Ramana-bharathi/satellite-housing-design-manufacturing/Drawings/DWG pics/Housing_bottom.jpg

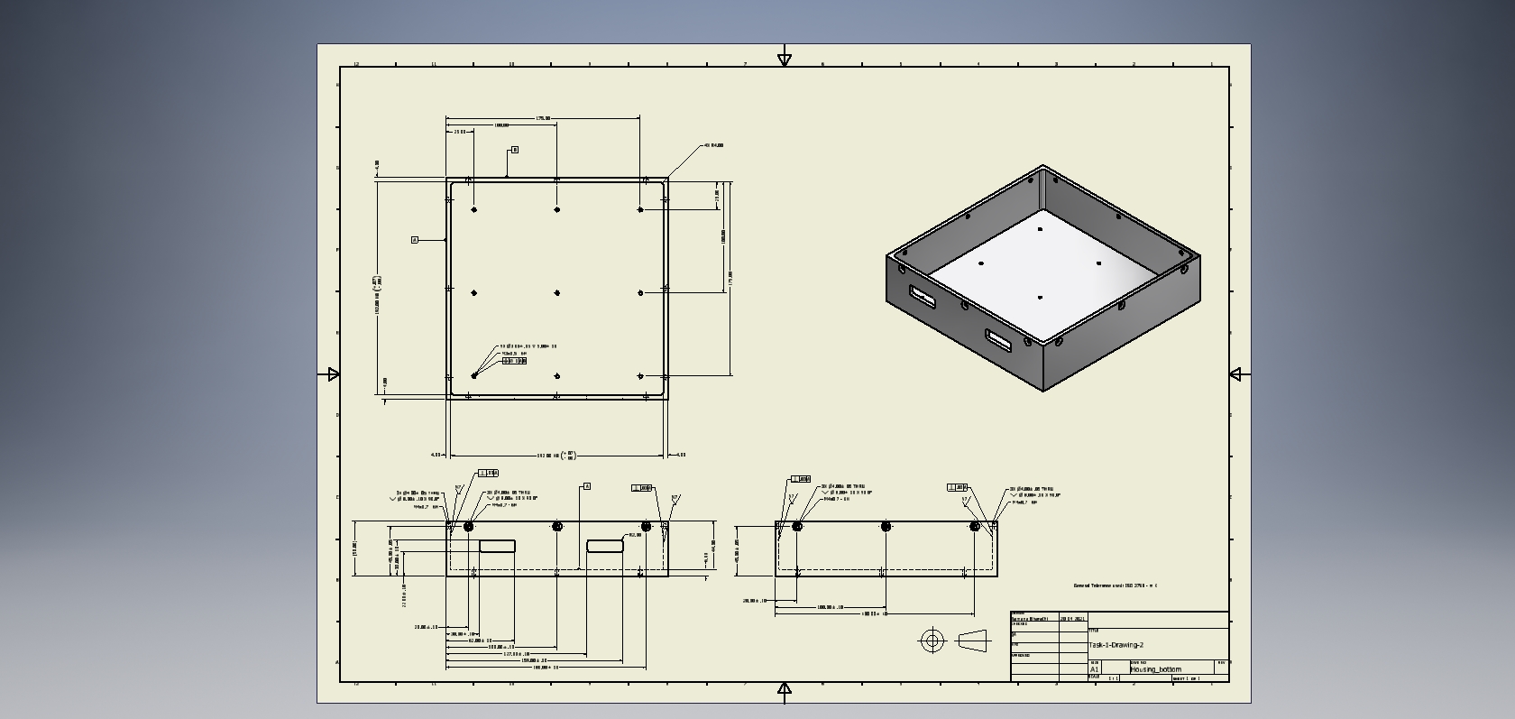
Drawings/DWG pics/Housing_bottom.jpg
