Ramana-bharathi/satellite-housing-design-manufacturing/Drawings/DWG pics/Housing_lid.jpg

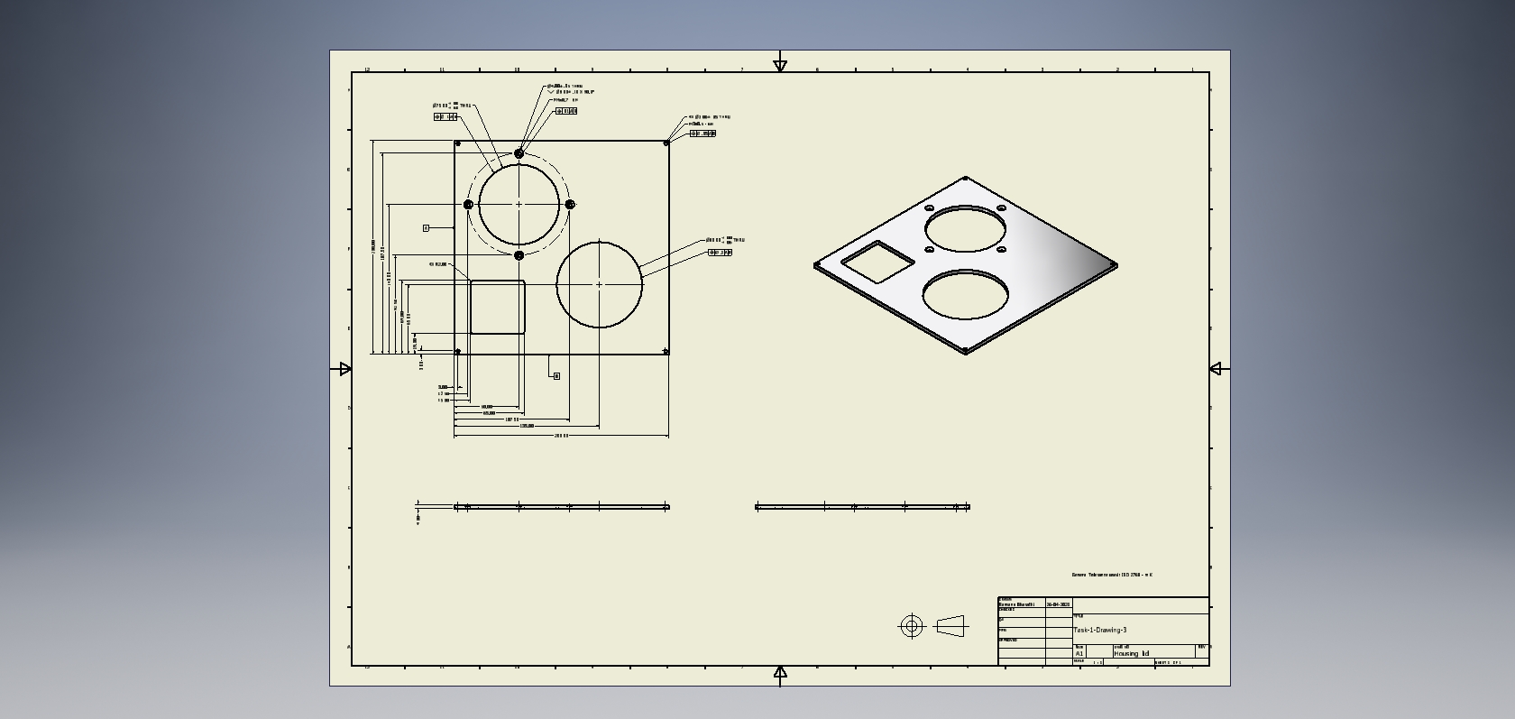
Drawings/DWG pics/Housing_lid.jpg
