Ramana-bharathi/satellite-housing-design-manufacturing/Drawings/DWG pics/Housing_top.jpg

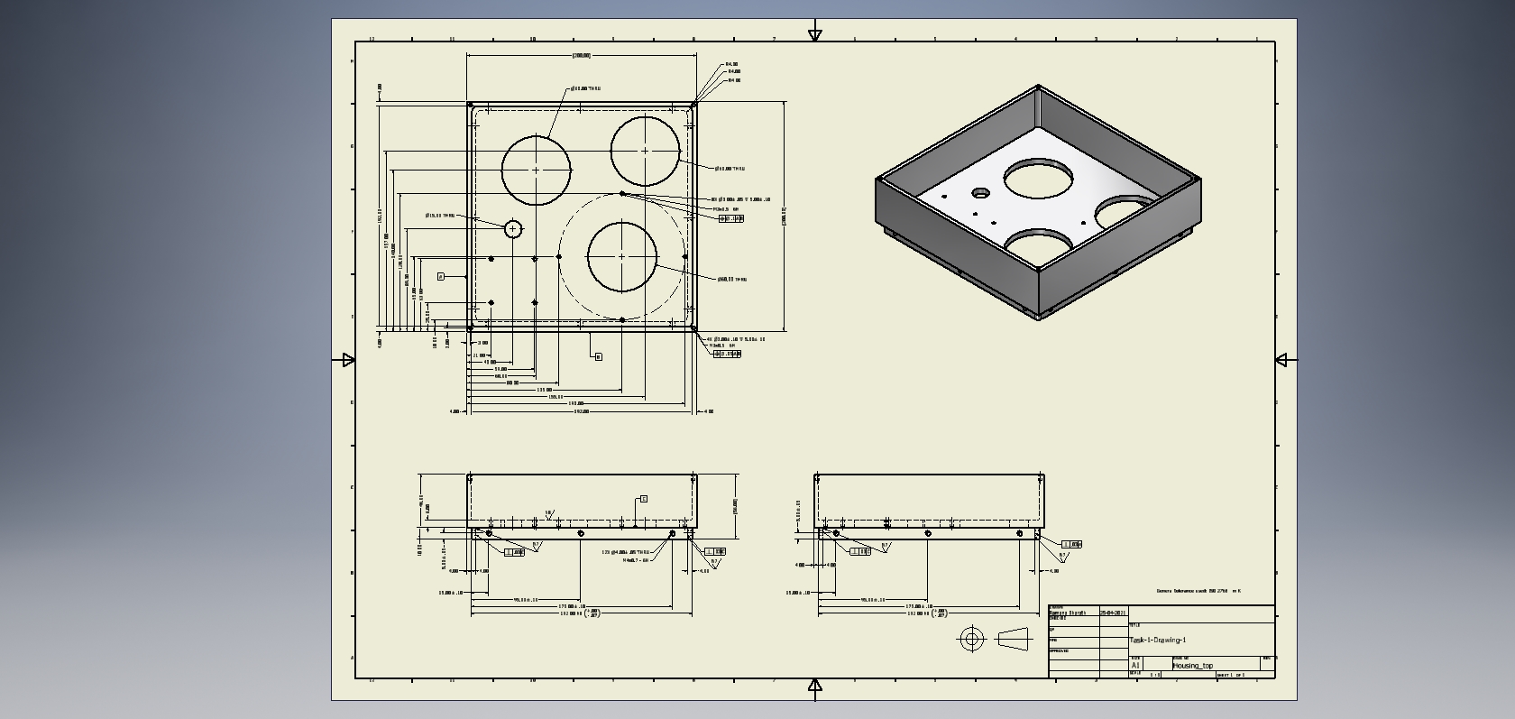
Drawings/DWG pics/Housing_top.jpg
