Ramana-bharathi/satellite-housing-design-manufacturing/Drawings/DWG pics/sensor1_lock.jpg

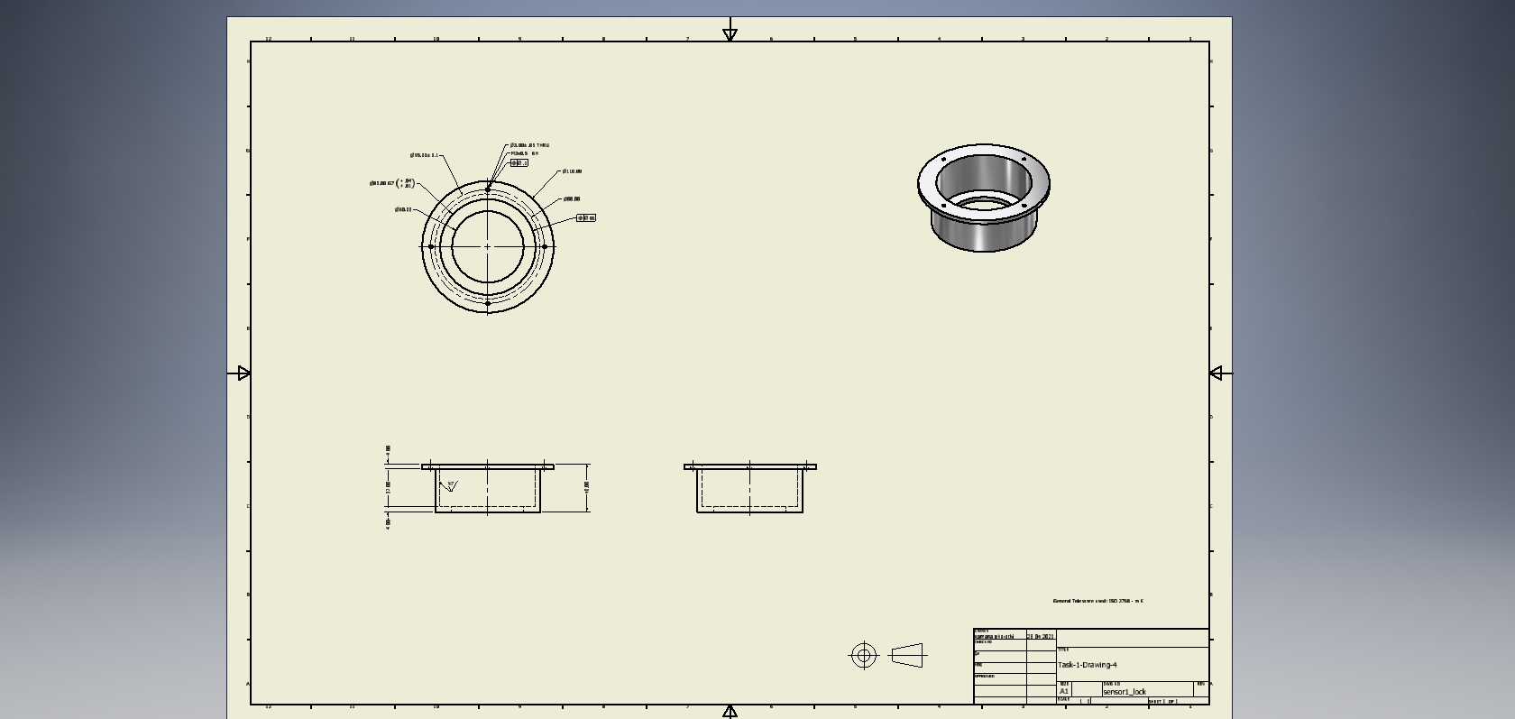
Drawings/DWG pics/sensor1_lock.jpg
