Ramana-bharathi/satellite-housing-design-manufacturing/Drawings/DWG pics/sensor2_lock.jpg

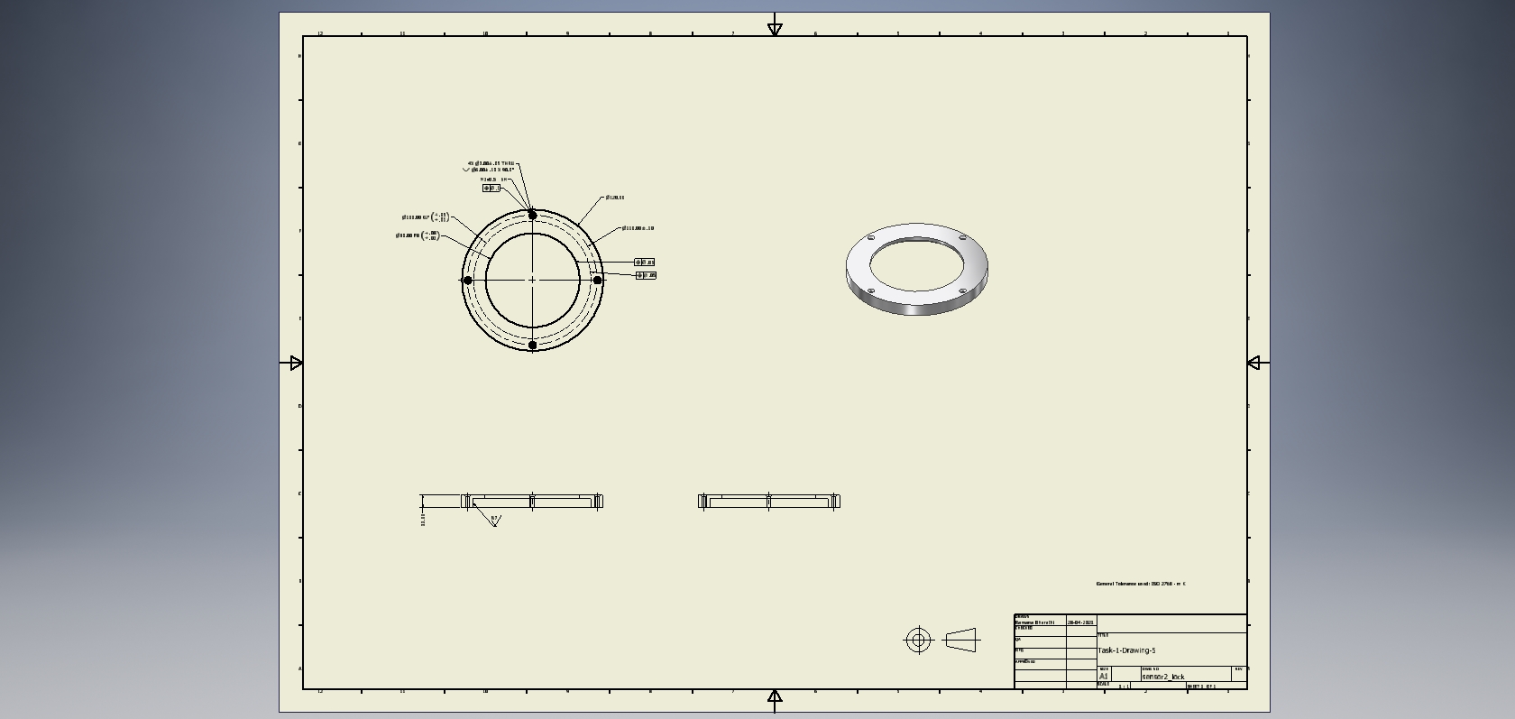
Drawings/DWG pics/sensor2_lock.jpg
