Ramana-bharathi/satellite-housing-design-manufacturing/Drawings/DWG pics/sensor3_lock.jpg

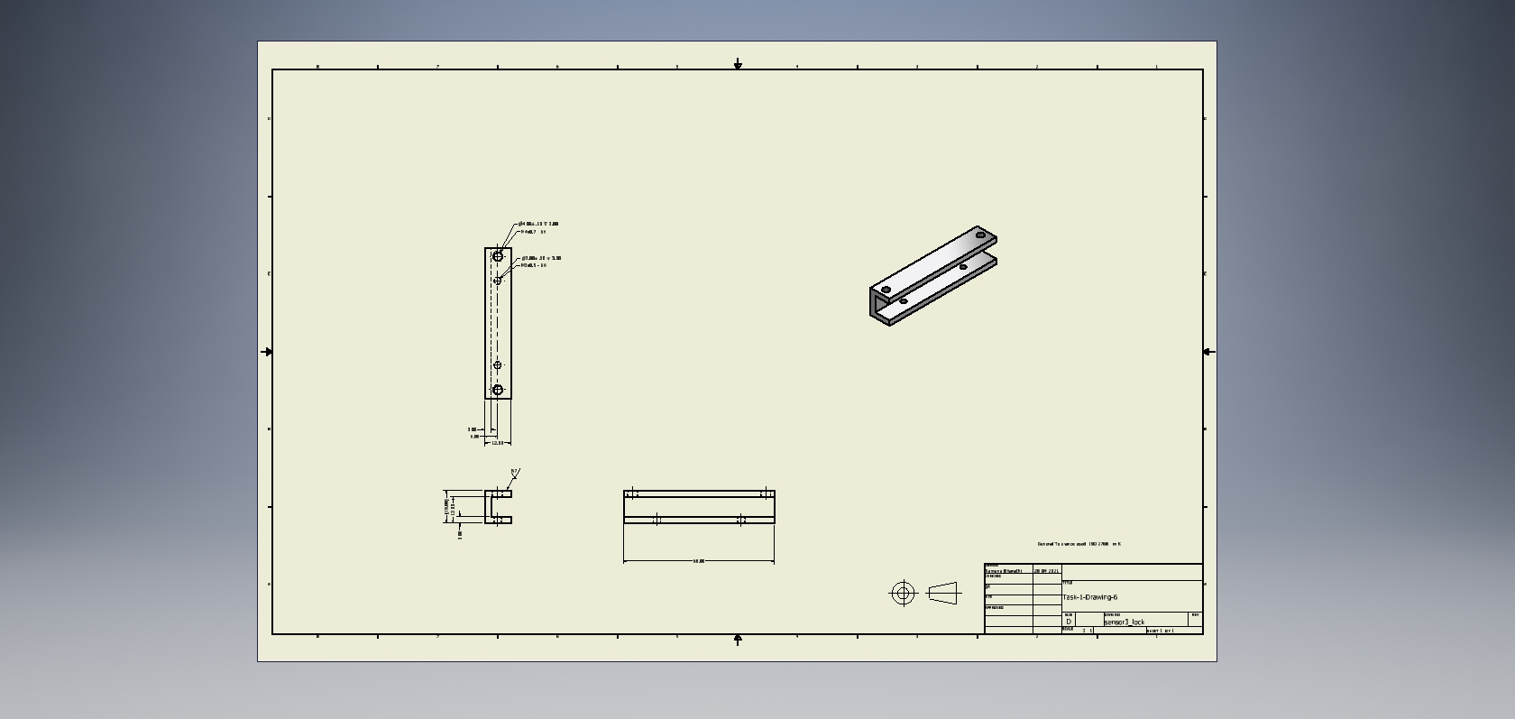
Drawings/DWG pics/sensor3_lock.jpg
