Ramana-bharathi/satellite-housing-design-manufacturing/Machining sequences/pics/housing_bottom-3.jpg

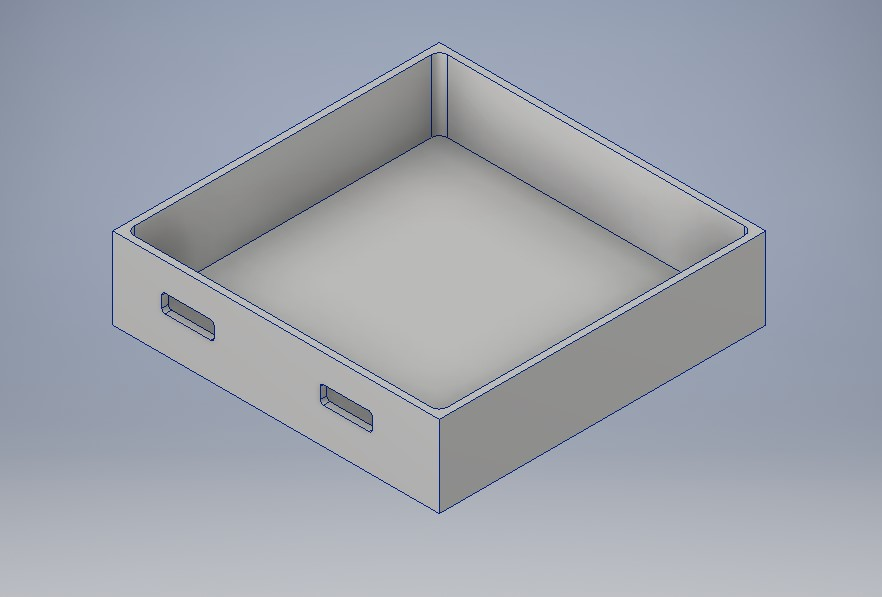
Machining sequences/pics/housing_bottom-3.jpg
