Ramana-bharathi/satellite-housing-design-manufacturing/Machining sequences/pics/housing_top-1.jpg

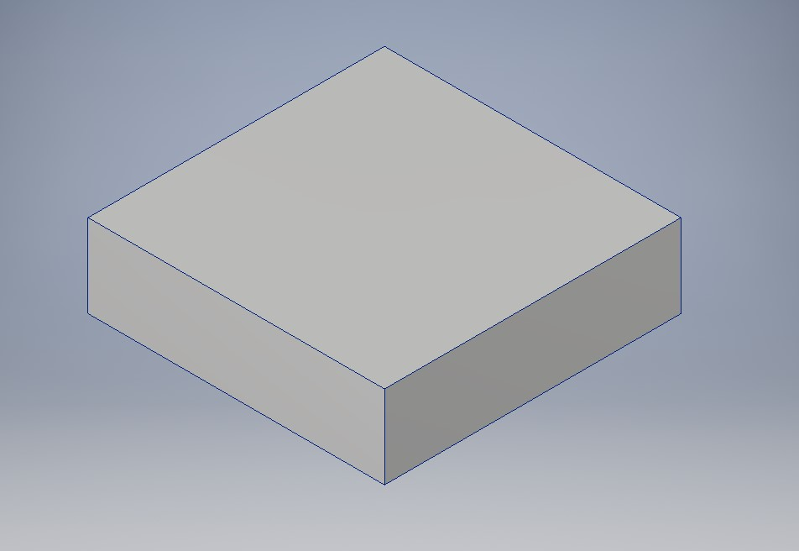
Machining sequences/pics/housing_top-1.jpg
