Ramana-bharathi/satellite-housing-design-manufacturing/Machining sequences/pics/housing_top-2a.jpg

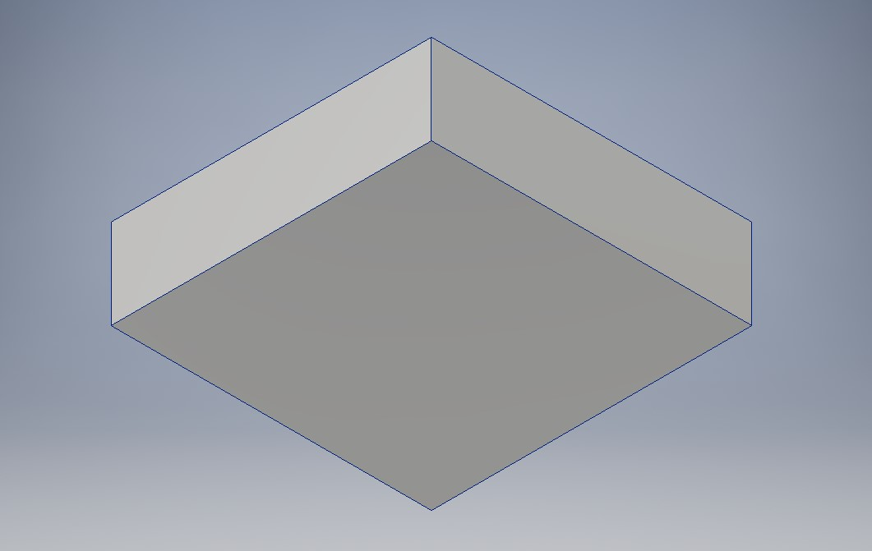
Machining sequences/pics/housing_top-2a.jpg
