Ramana-bharathi/satellite-housing-design-manufacturing/Machining sequences/pics/housing_top-5.jpg

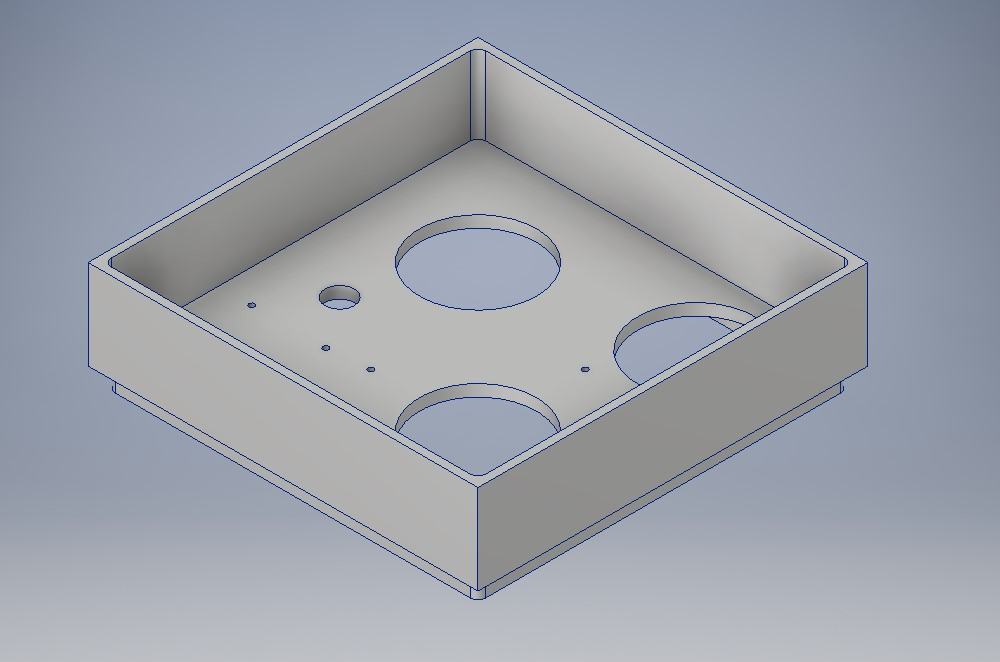
Machining sequences/pics/housing_top-5.jpg
