Ramana-bharathi/satellite-housing-design-manufacturing/Machining sequences/pics/housing_top-7a.jpg

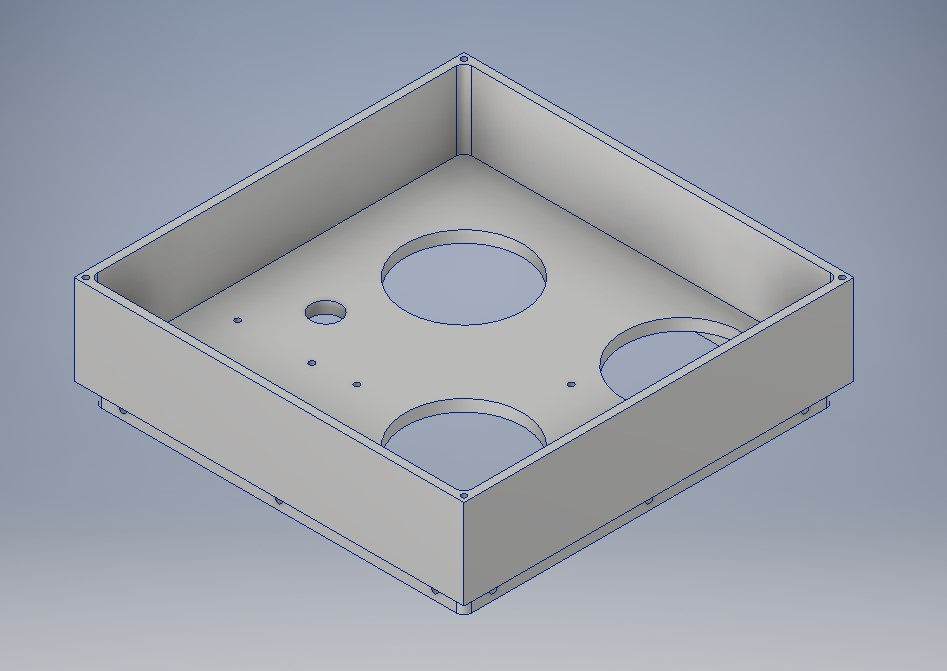
Machining sequences/pics/housing_top-7a.jpg
