Ramana-bharathi/satellite-housing-design-manufacturing/Machining sequences/pics/sensor1_lock-2.jpg

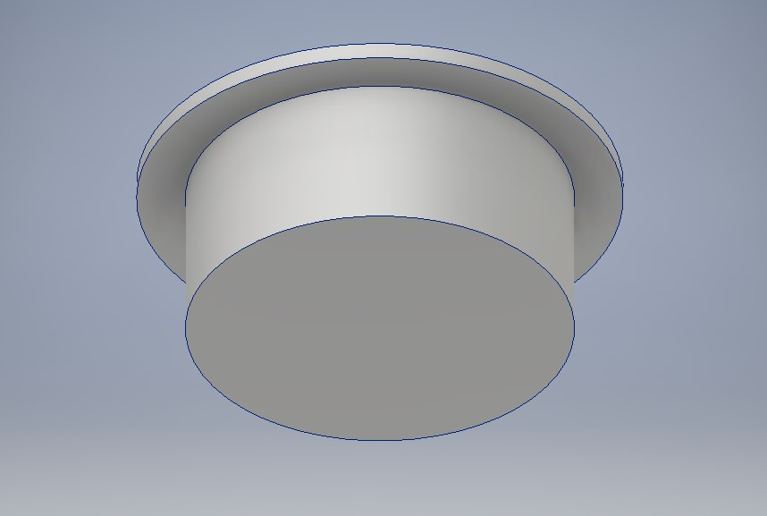
Machining sequences/pics/sensor1_lock-2.jpg
