Ramana-bharathi/satellite-housing-design-manufacturing/Machining sequences/pics/sensor1_lock-5.jpg

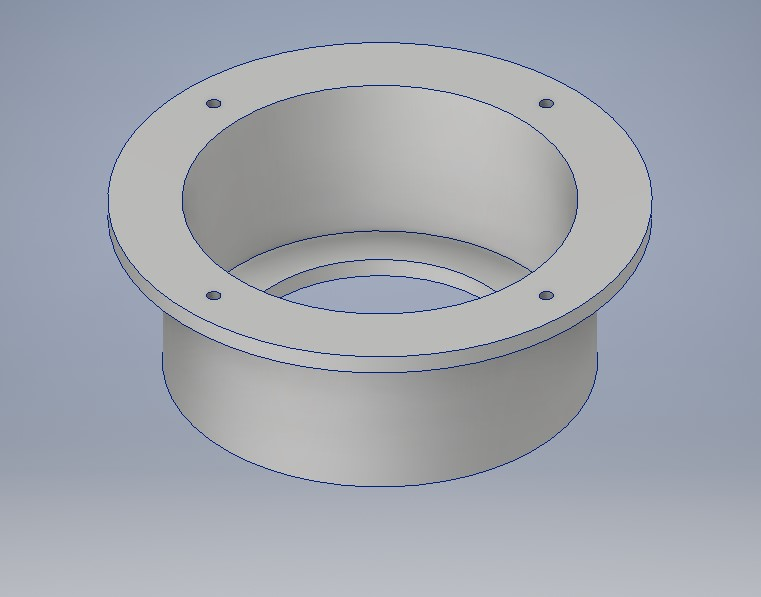
Machining sequences/pics/sensor1_lock-5.jpg
