Ramana-bharathi/satellite-housing-design-manufacturing/Machining sequences/pics/sensor2_lock-3a.jpg

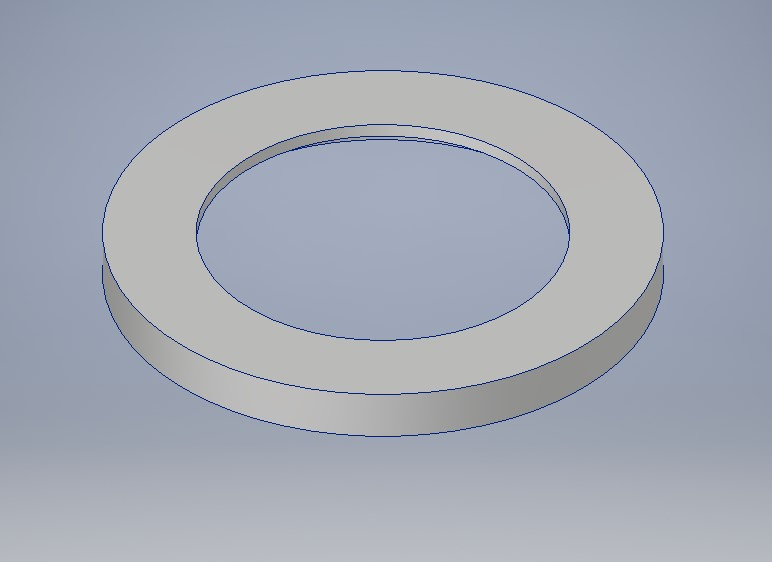
Machining sequences/pics/sensor2_lock-3a.jpg
