Ramana-bharathi/satellite-housing-design-manufacturing/Machining sequences/pics/sensor3_lock-4.jpg

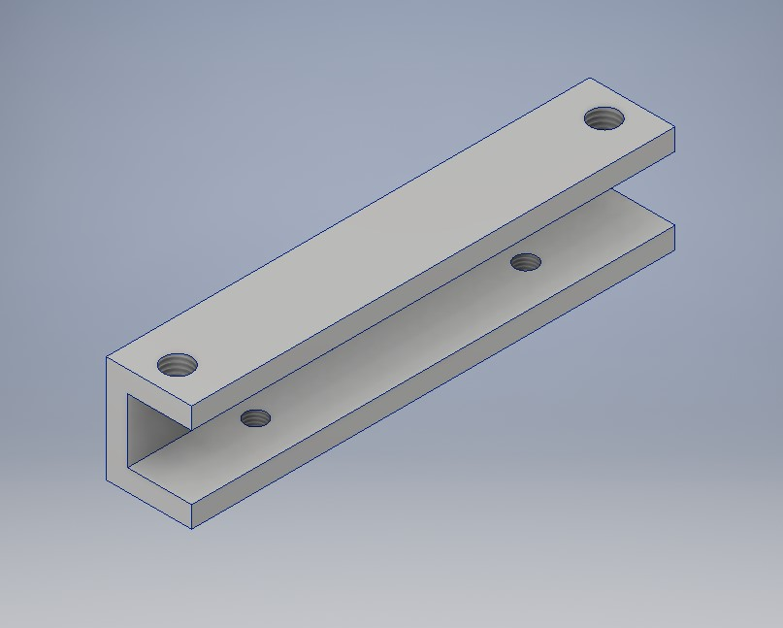
Machining sequences/pics/sensor3_lock-4.jpg
