Ramana-bharathi/satellite-housing-design-manufacturing/pics/Board.jpg

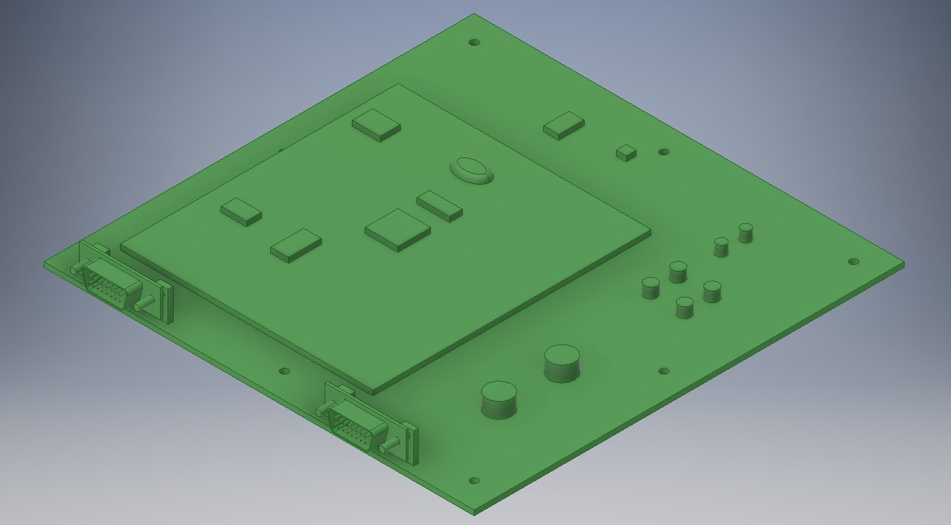
pics/Board.jpg
