Ramana-bharathi/satellite-housing-design-manufacturing/pics/Housing_bottom.jpg

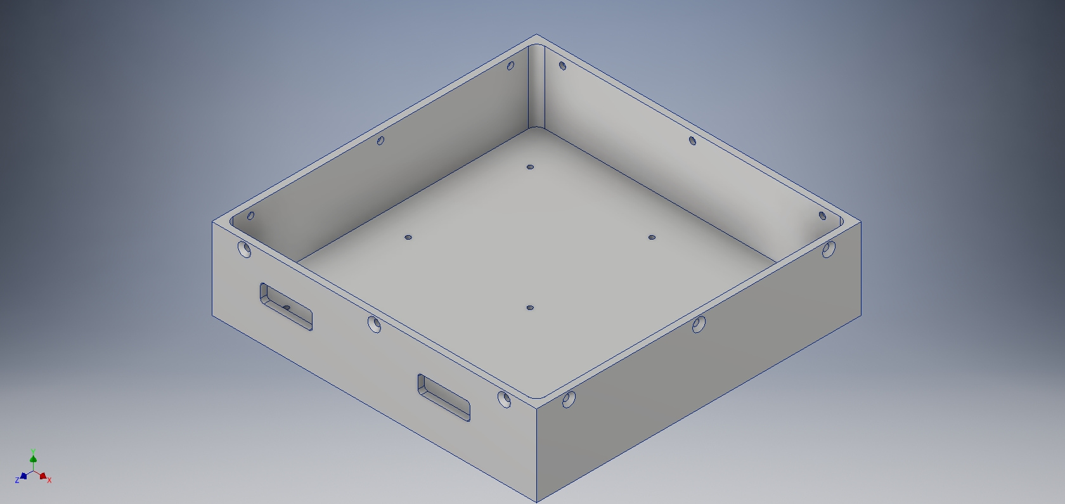
pics/Housing_bottom.jpg
