Ramana-bharathi/satellite-housing-design-manufacturing/pics/Housing_top_assmebled.jpg

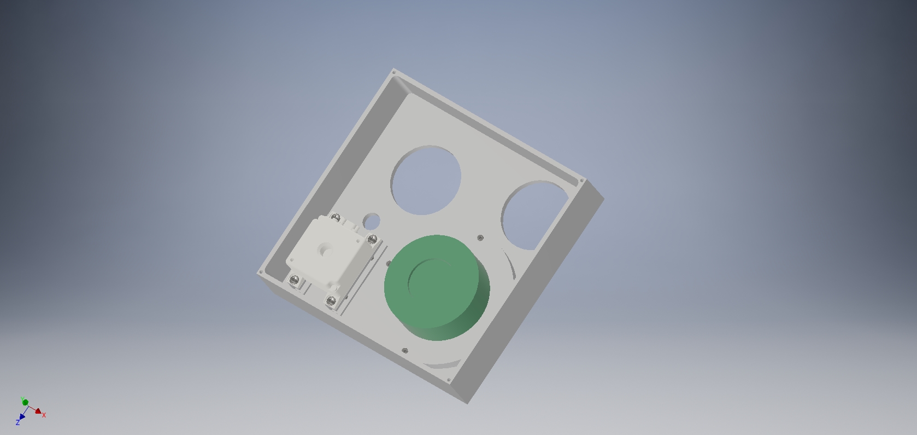
pics/Housing_top_assmebled.jpg
