Ramana-bharathi/satellite-housing-design-manufacturing/pics/sensor1.jpg

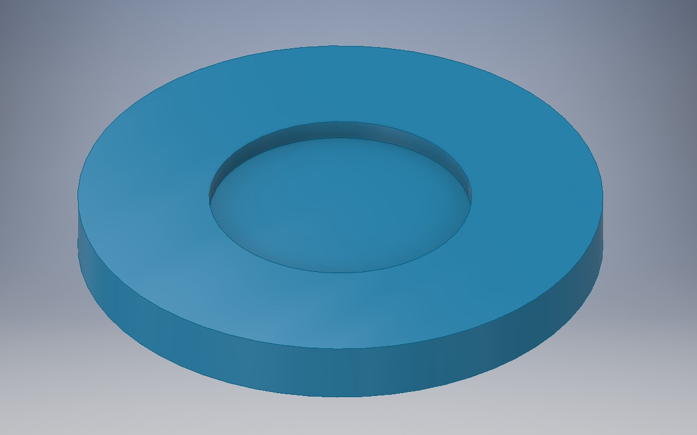
pics/sensor1.jpg
