Ramana-bharathi/satellite-housing-design-manufacturing/pics/sensor2.jpg

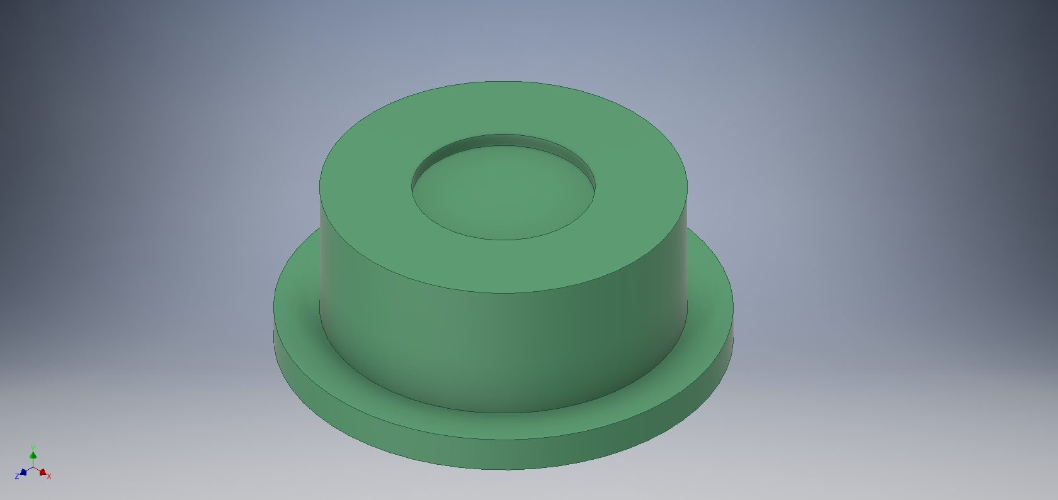
pics/sensor2.jpg
