Ramana-bharathi/satellite-housing-design-manufacturing/pics/sensor3.jpg

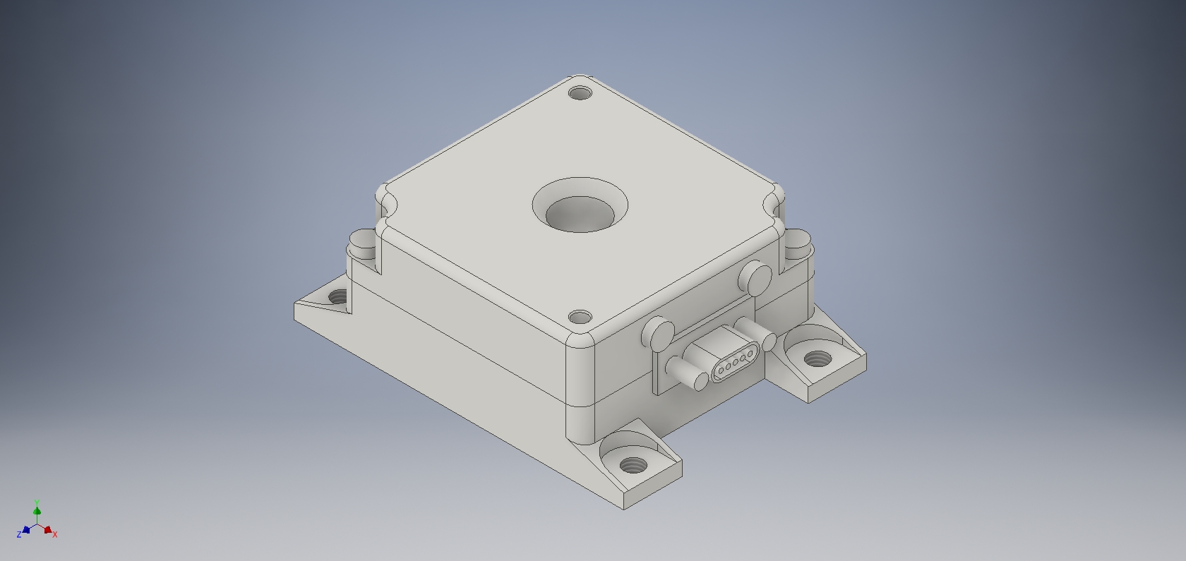
pics/sensor3.jpg
