Ramana-bharathi/satellite-housing-design-manufacturing/STEP files/sensor2_lock.stp

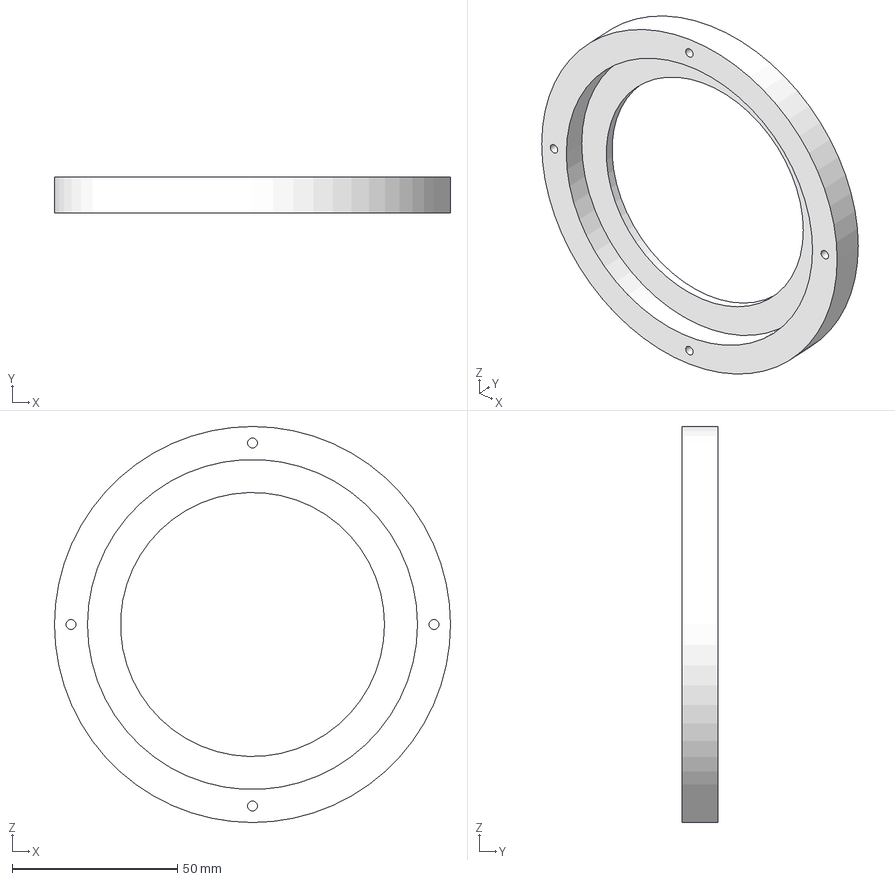
[picture p83: CAD file, 2021-11-17]
STEP files/sensor2_lock.stp
120.0 x 11.0 x 120.0 mm
