Ramana-bharathi/satellite-housing-design-manufacturing/STEP files/Board.stp

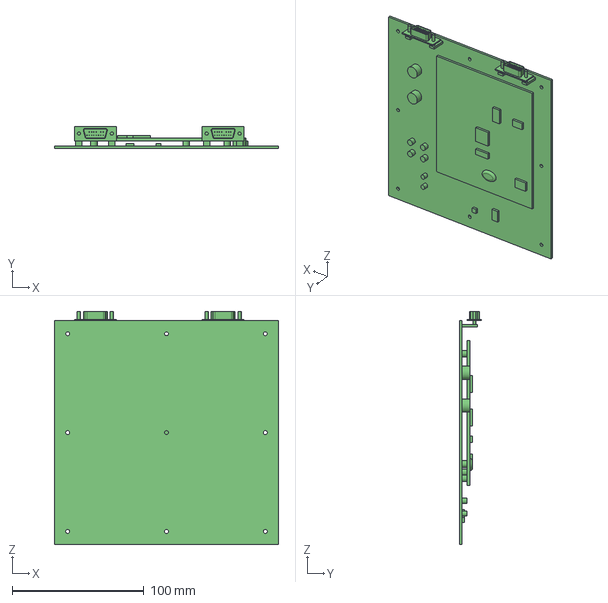
[picture p84: CAD file, 2021-11-17]
STEP files/Board.stp
170.0 x 17.0 x 177.0 mm
