Ramana-bharathi/satellite-housing-design-manufacturing/STEP files/sensor1_lock.stp

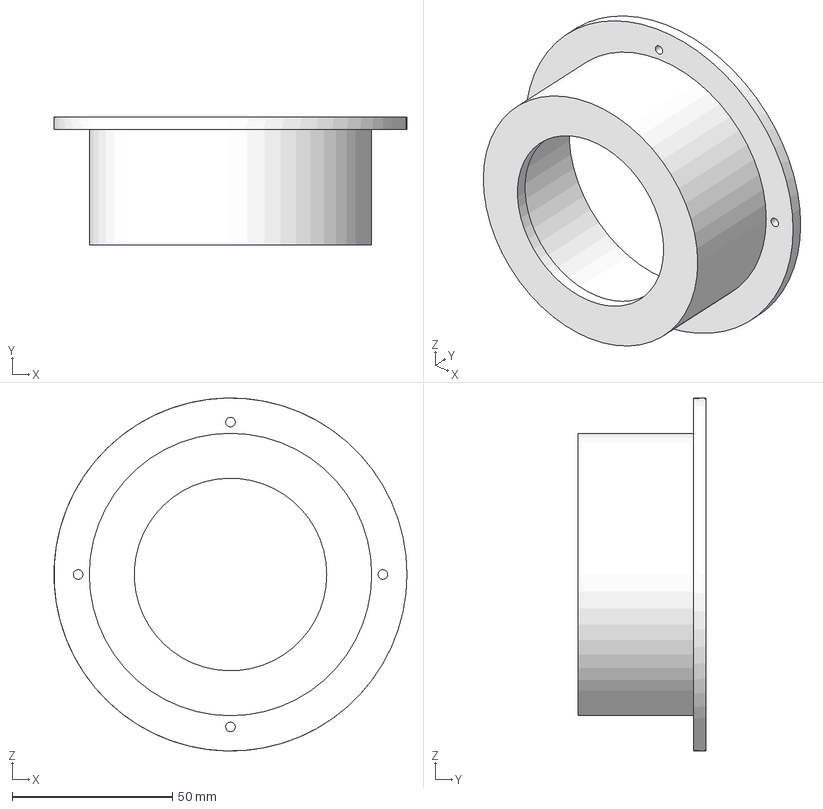
[picture p85: CAD file, 2021-11-17]
STEP files/sensor1_lock.stp
110.0 x 40.0 x 110.0 mm
