Ramana-bharathi/satellite-housing-design-manufacturing/STEP files/Housing_top.stp

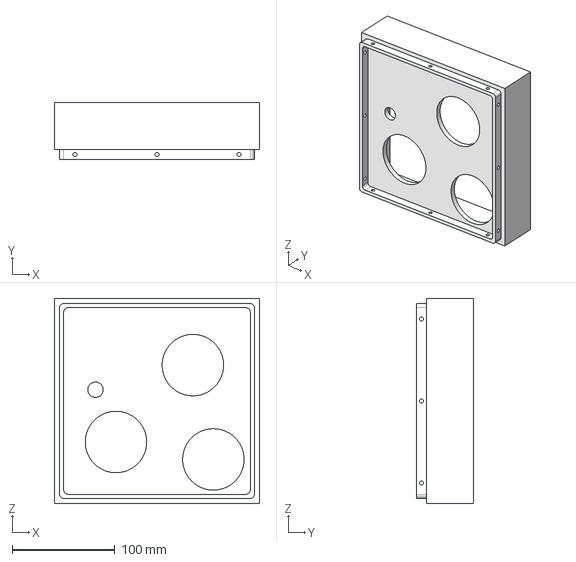
[picture p86: CAD file, 2021-11-17]
STEP files/Housing_top.stp
200.0 x 56.0 x 200.0 mm
