Ramana-bharathi/satellite-housing-design-manufacturing/STEP files/sensor1.stp

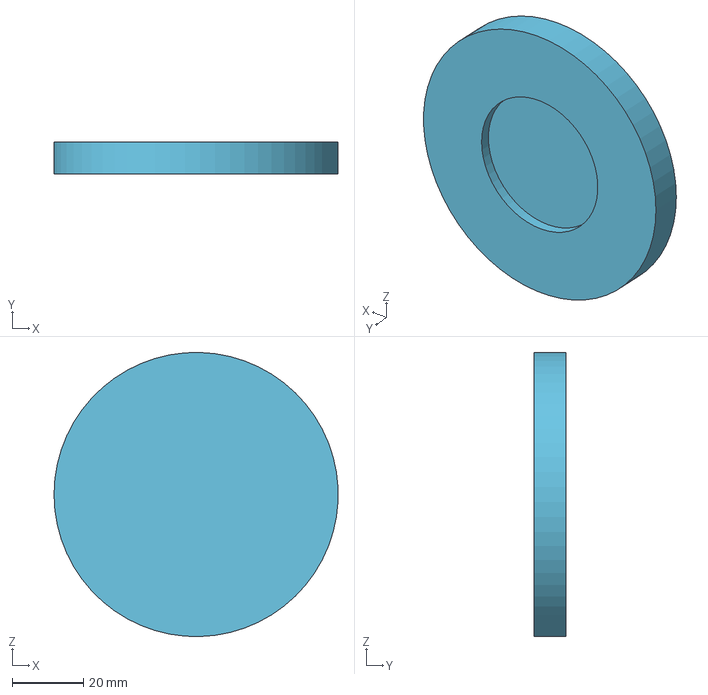
[picture p87: CAD file, 2021-11-17]
STEP files/sensor1.stp
79.9 x 9.00 x 80.0 mm
