Ramana-bharathi/satellite-housing-design-manufacturing/STEP files/sensor3_lock.stp

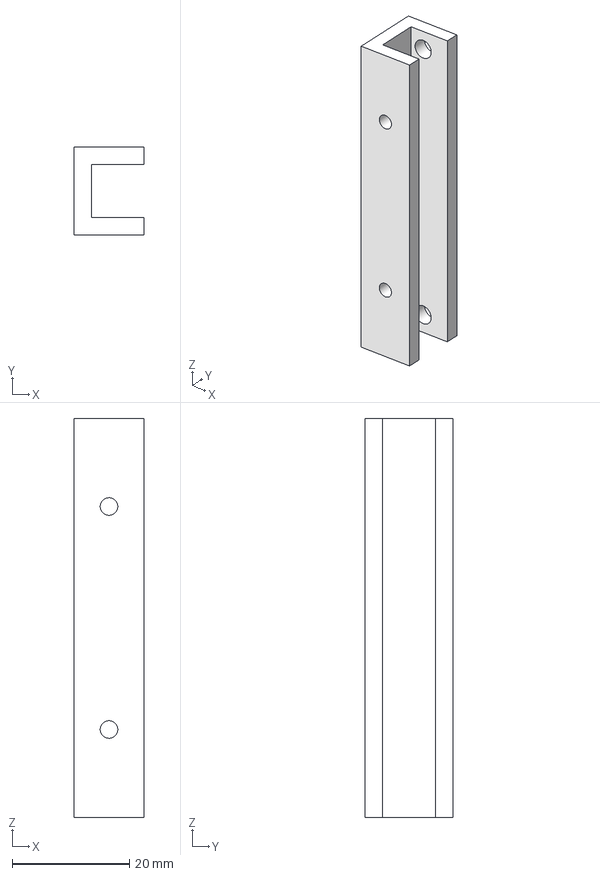
[picture p88: CAD file, 2021-11-17]
STEP files/sensor3_lock.stp
12.0 x 15.0 x 68.0 mm
