Ramana-bharathi/satellite-housing-design-manufacturing/pics/Housing_lid_assembled.jpg

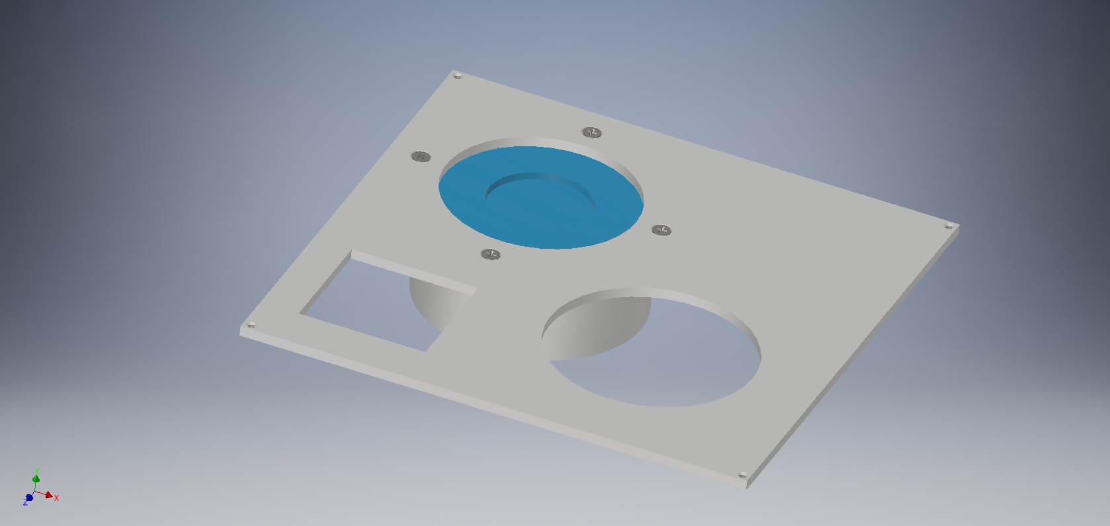
pics/Housing_lid_assembled.jpg
