Ramana-bharathi/satellite-housing-design-manufacturing/Drawings/DWG PDFs/Housing_bottom.pdf

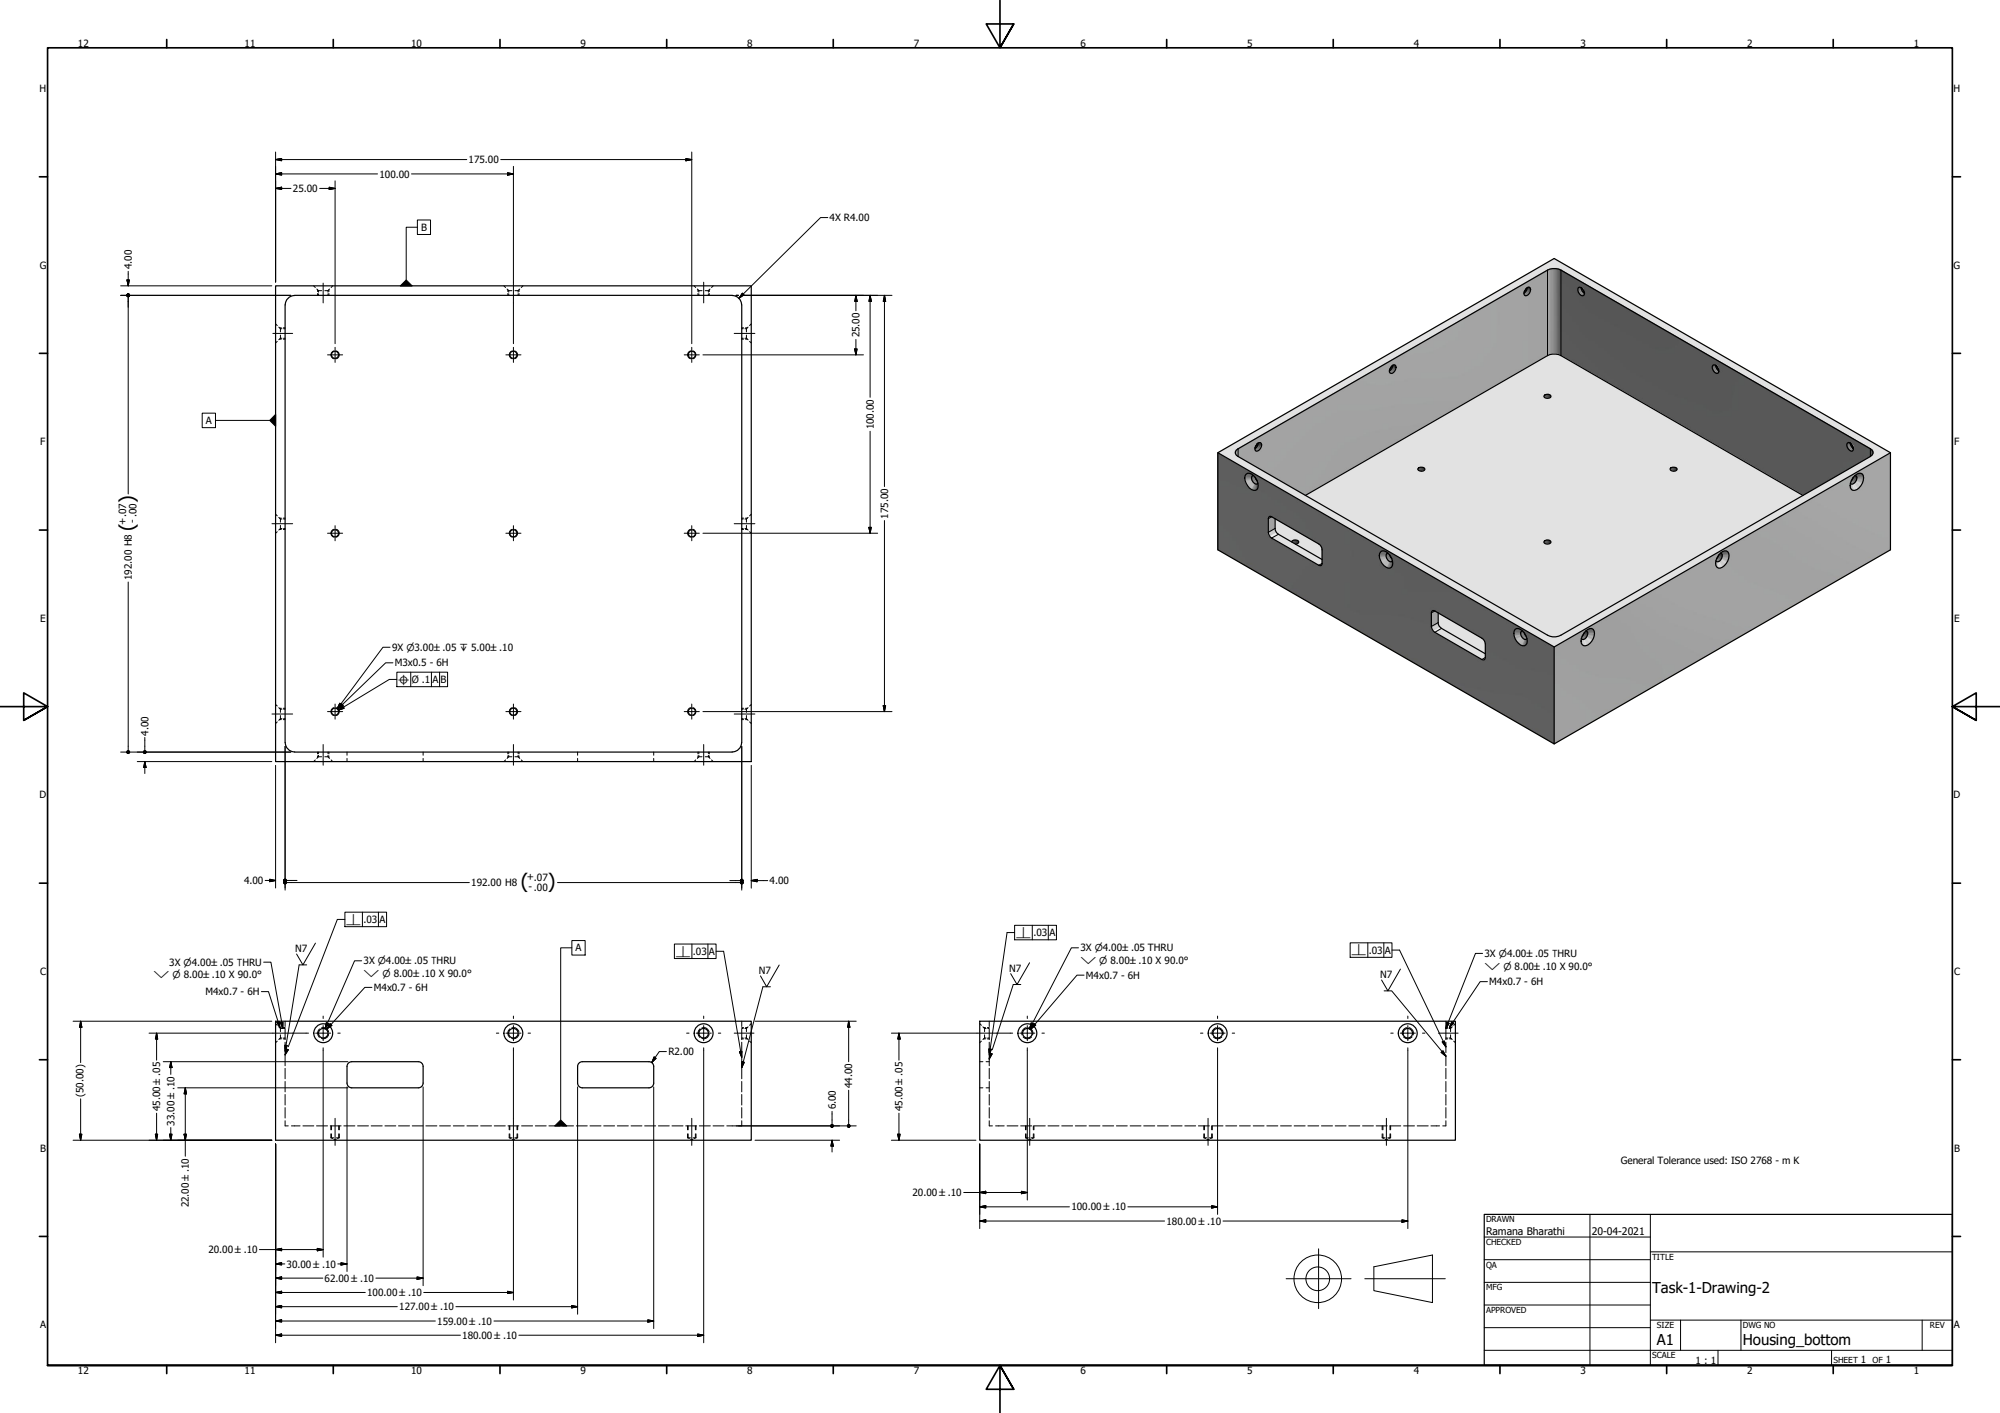
[picture p90: page 1]

General Tolerance used: ISO 2768 - m K

DRAWN Ramana Bharathi | 20-04-2021

CHECKED

MFG

APPROVED

SIZE A1 | DWG NO Housing_bottom | REV

SCALE 1 : 1 | | SHEET 1 OF 1
