Ramana-bharathi/satellite-housing-design-manufacturing/Drawings/DWG PDFs/Housing_lid.pdf

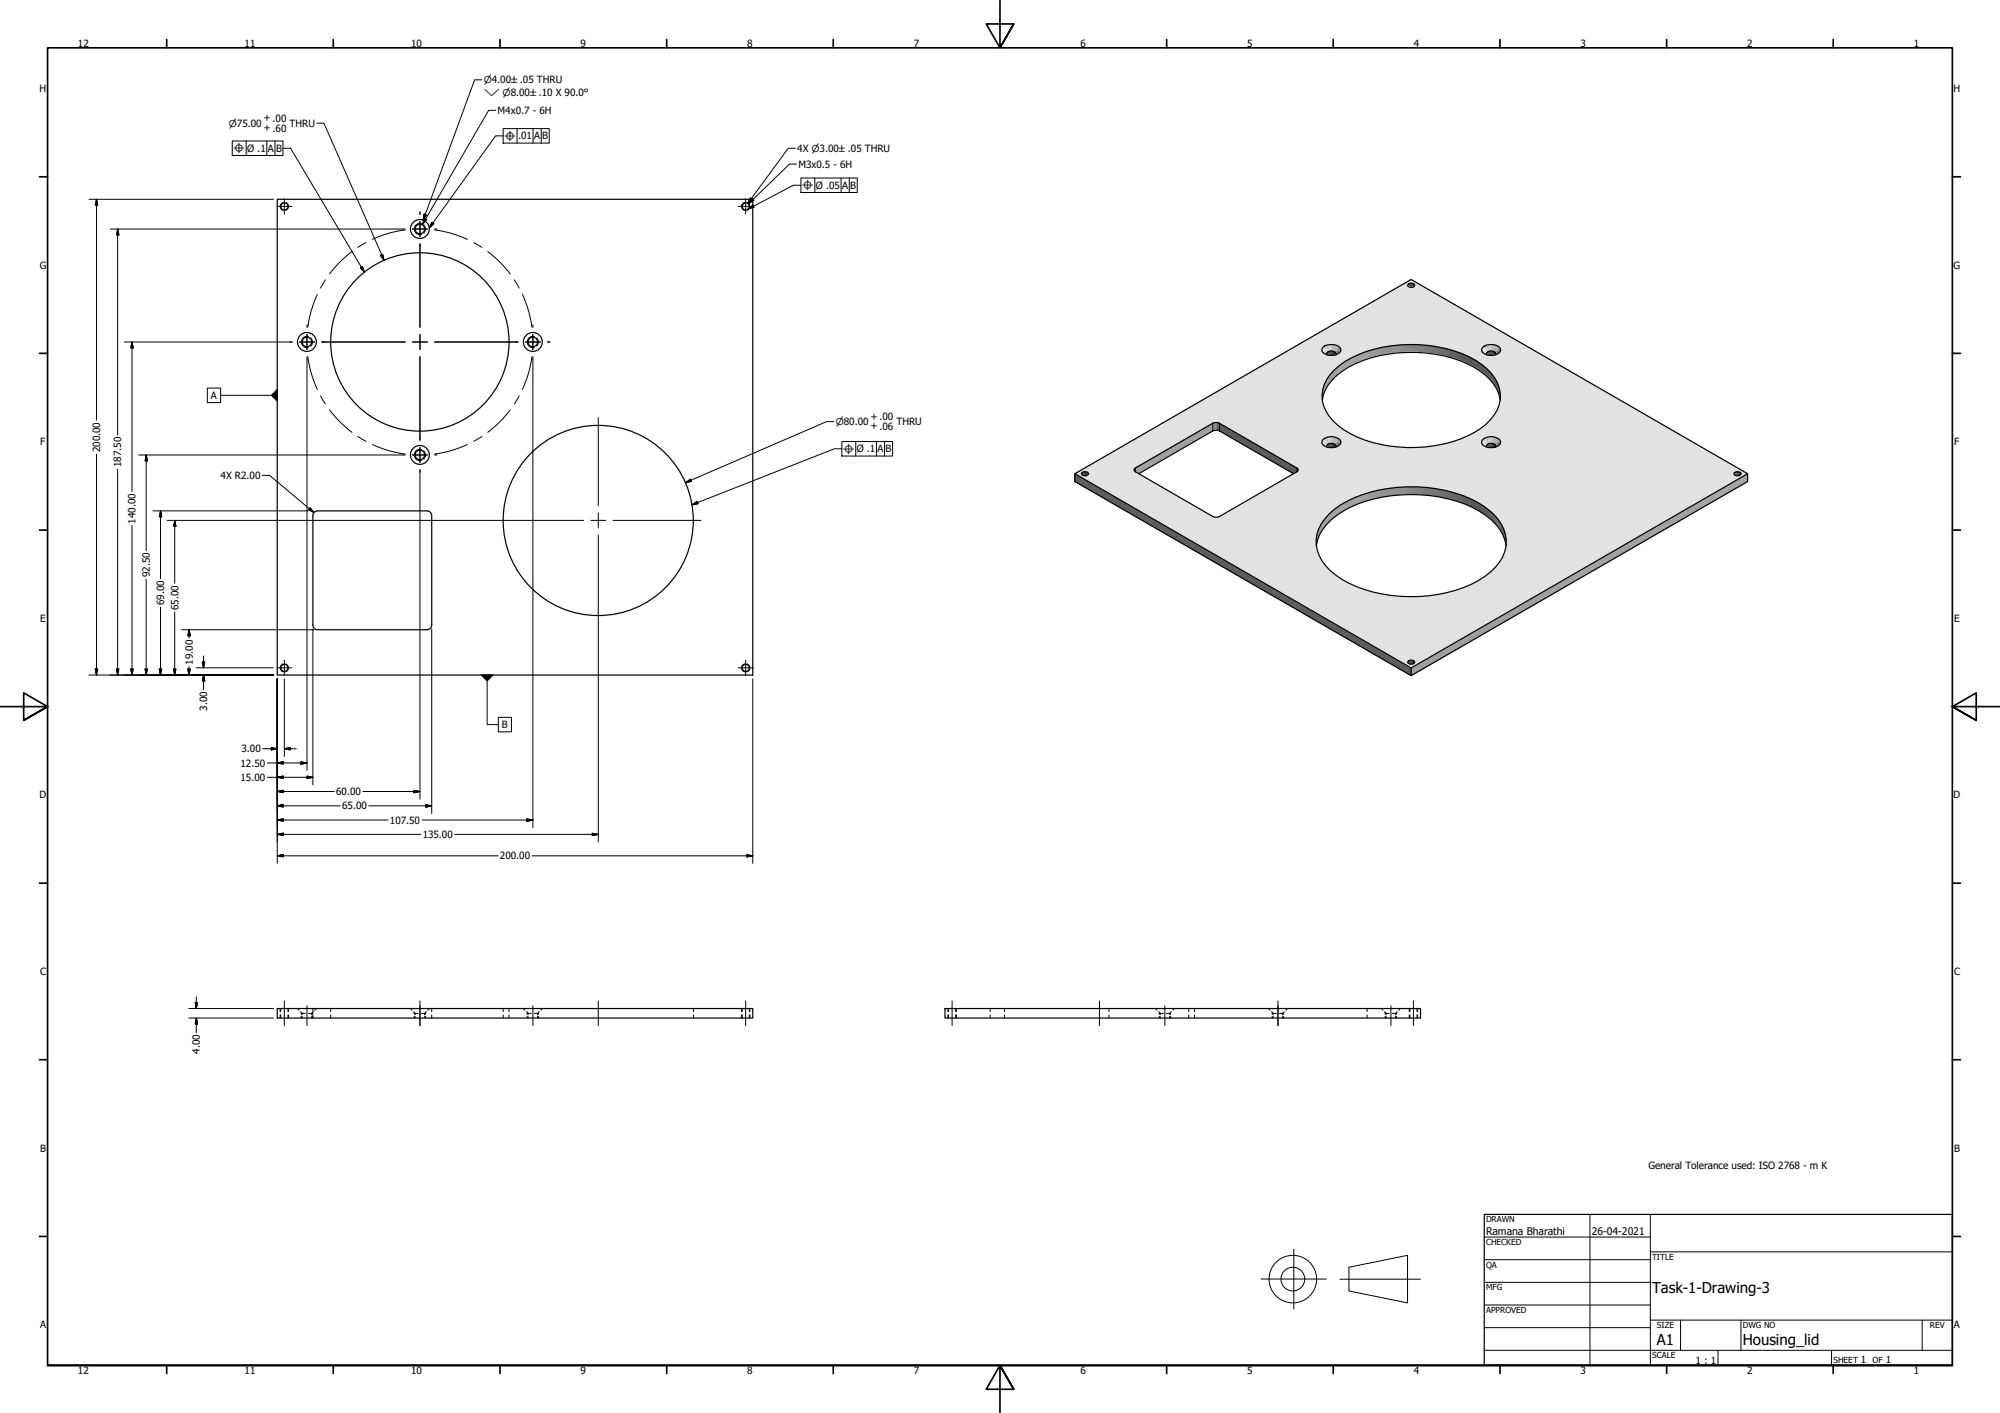
[picture p91: page 1]

General Tolerance used: ISO 2768 - m K

DRAWN Ramana Bharathi | 26-04-2021

CHECKED

MFG

APPROVED

SIZE A1 | DWG NO Housing_lid | REV

SCALE 1 : 1 | | SHEET 1 OF 1
