Ramana-bharathi/satellite-housing-design-manufacturing/Drawings/DWG PDFs/Housing_top.pdf

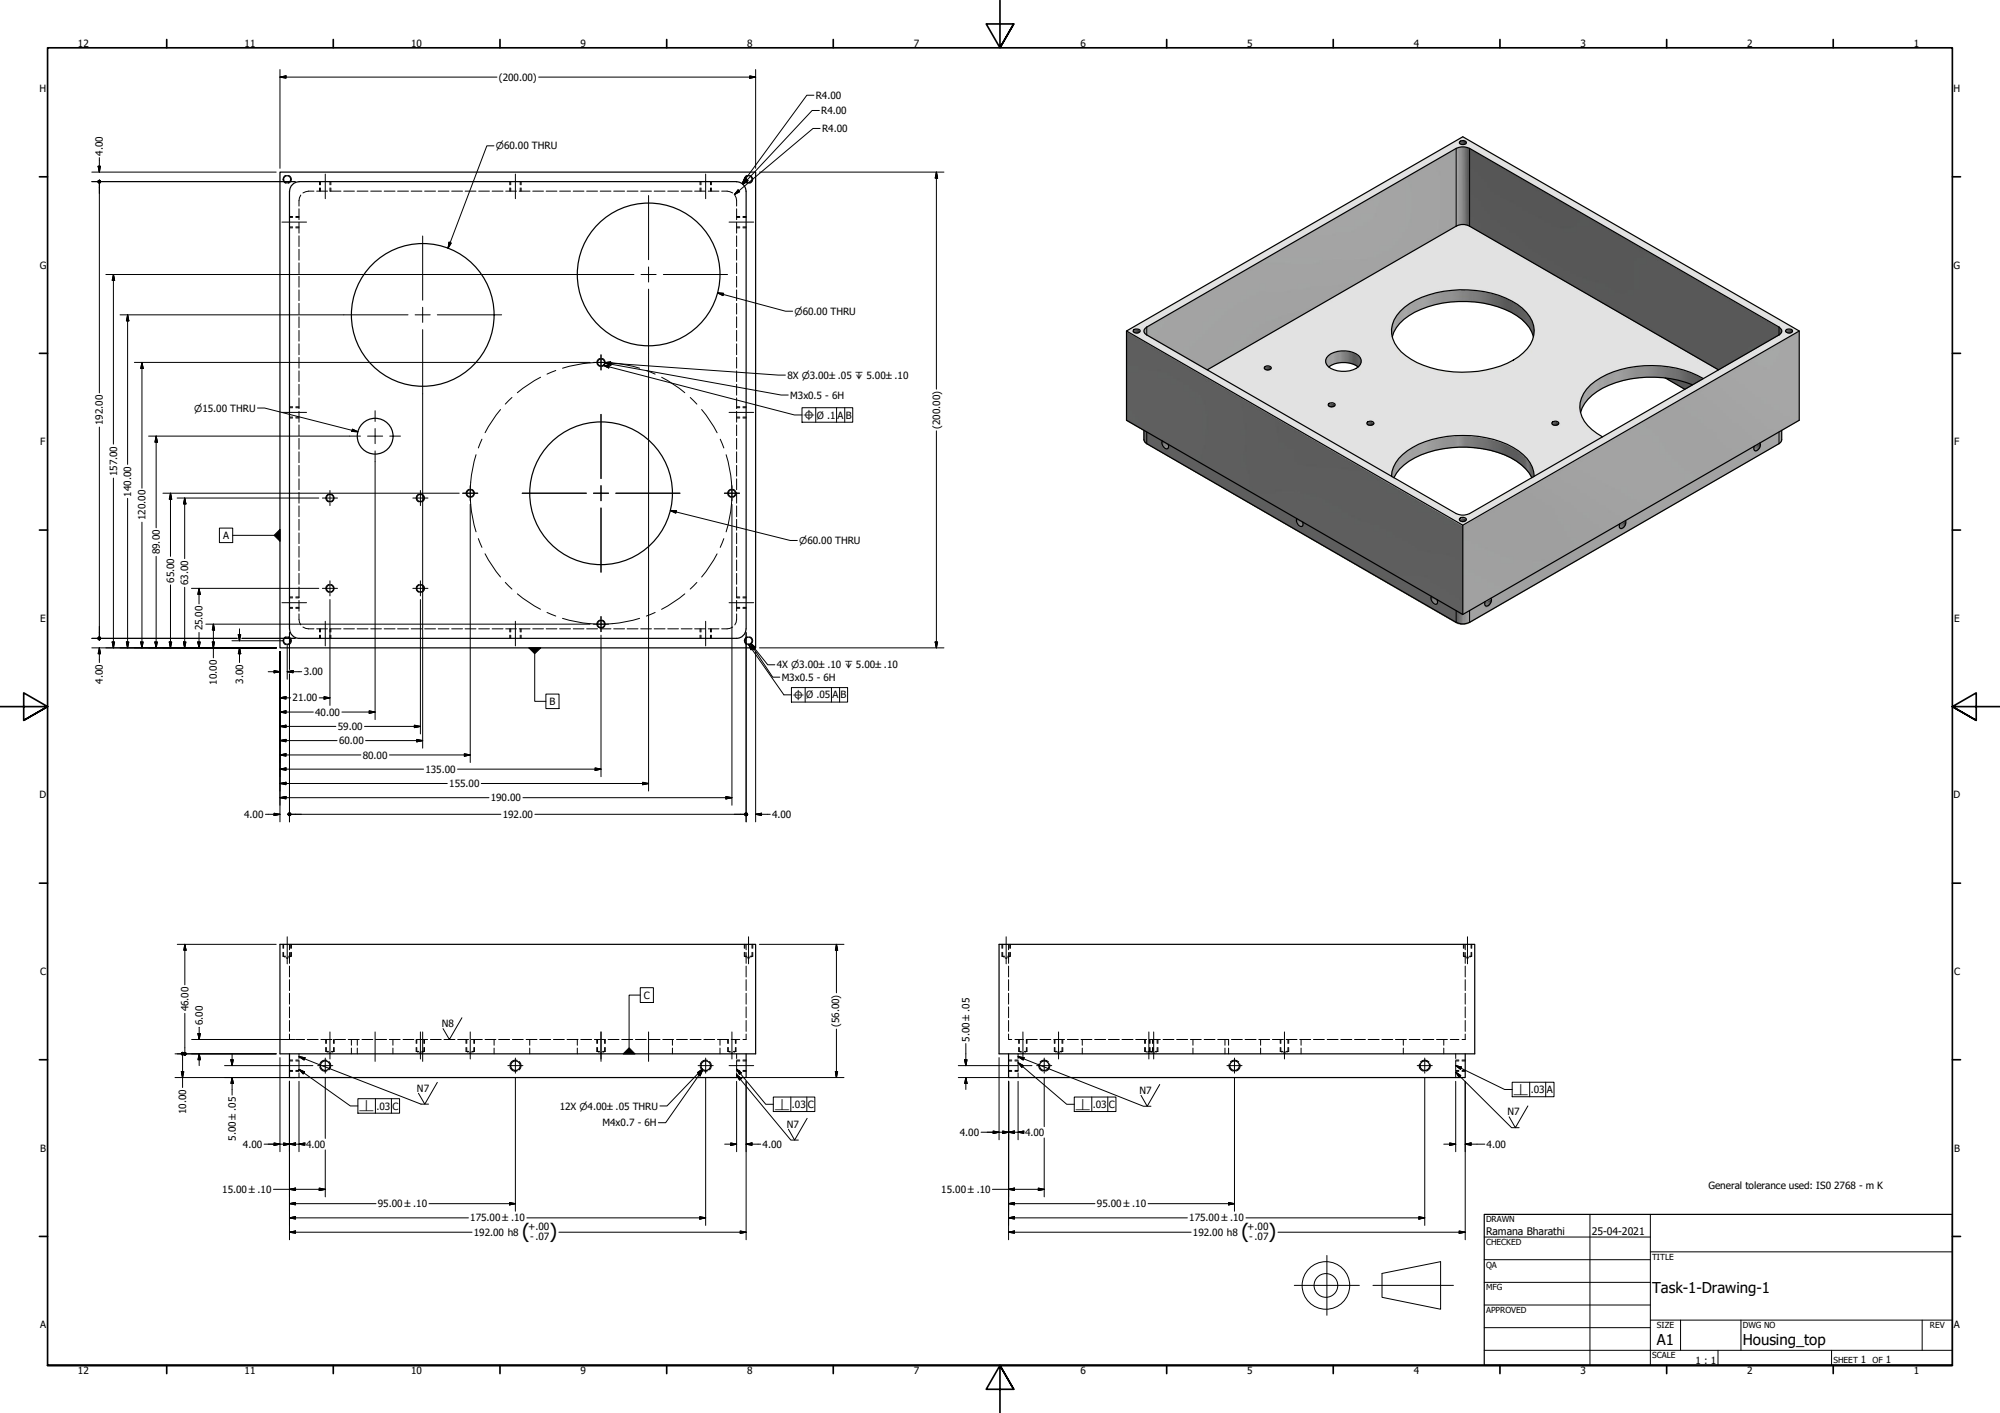
[picture p92: page 1]

General tolerance used: IS0 2768 - m K

DRAWN Ramana Bharathi | 25-04-2021

CHECKED

MFG

APPROVED

SIZE A1 | DWG NO Housing_top | REV

SCALE 1 : 1 | | SHEET 1 OF 1
