Ramana-bharathi/satellite-housing-design-manufacturing/Drawings/DWG PDFs/sensor1_lock.pdf

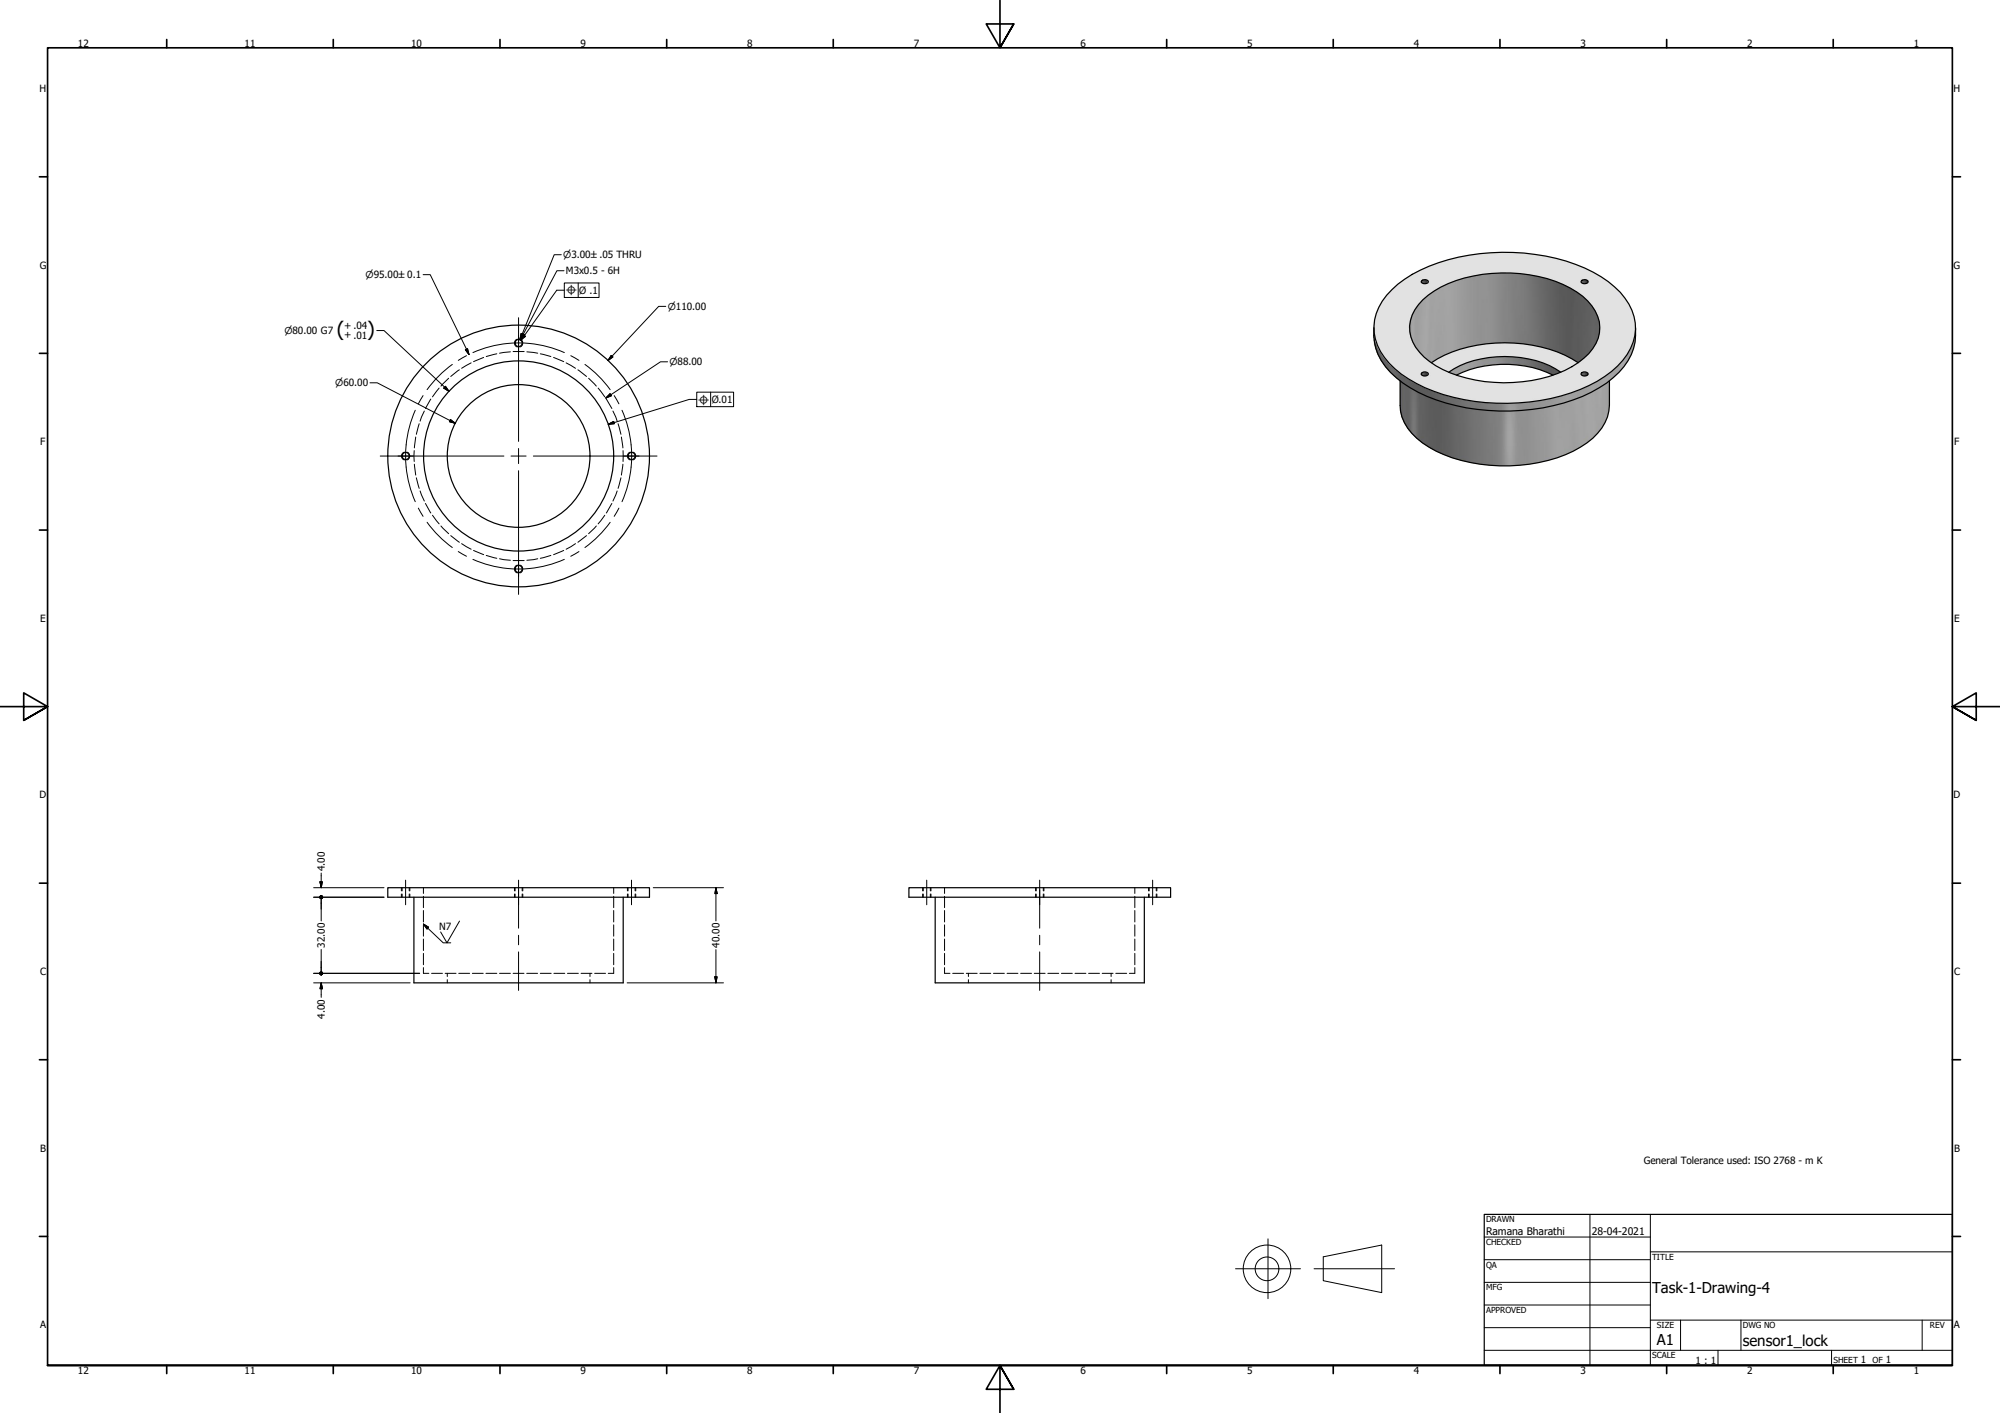
[picture p93: page 1]

General Tolerance used: ISO 2768 - m K

DRAWN Ramana Bharathi | 28-04-2021

CHECKED

MFG

APPROVED

SIZE A1 | DWG NO sensor1_lock | REV

SCALE 1 : 1 | | SHEET 1 OF 1
