Ramana-bharathi/satellite-housing-design-manufacturing/Drawings/DWG PDFs/sensor3_lock.pdf

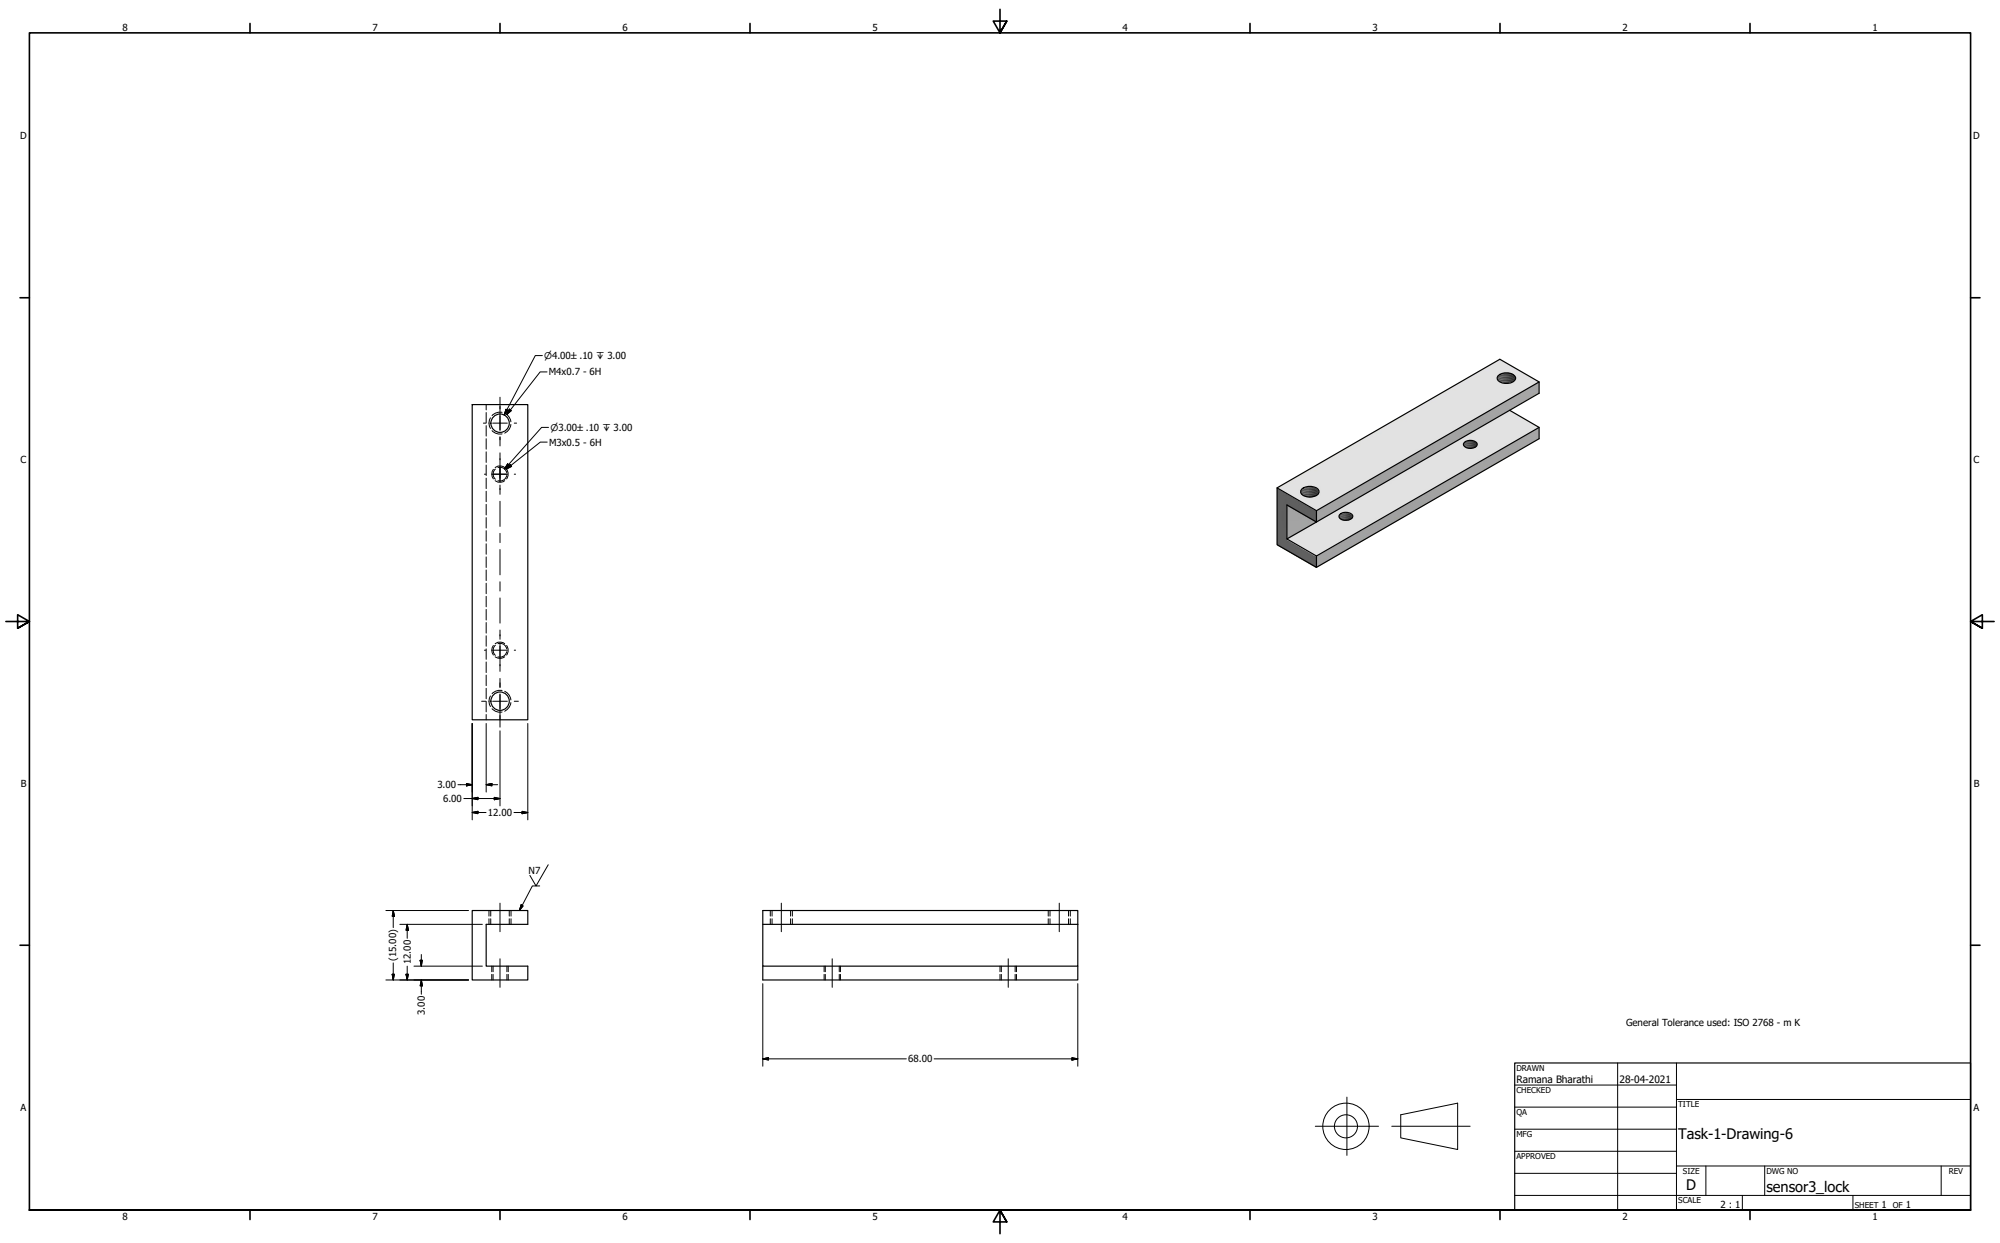
[picture p95: page 1]

General Tolerance used: ISO 2768 - m K

DRAWN Ramana Bharathi | 28-04-2021

CHECKED

MFG

APPROVED

SIZE D | DWG NO sensor3_lock | REV

SCALE 2 : 1 | | SHEET 1 OF 1
